zugaldia/cubo/stl/cubo_mounting_plate_vesa.stl

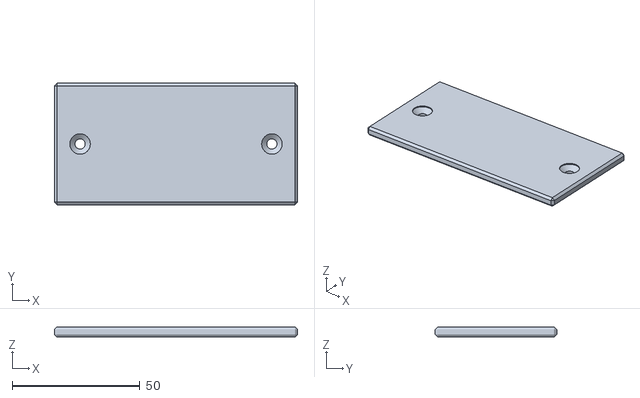
[picture p44: CAD file, 2023-10-19]
stl/cubo_mounting_plate_vesa.stl
95.0 x 47.5 x 4.00
