zugaldia/cubo/stl/cubo_grid_flatiron_small.stl

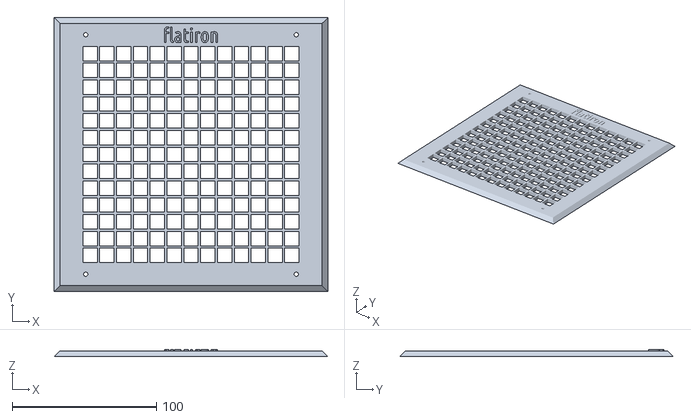
[picture p45: CAD file, 2023-10-19]
stl/cubo_grid_flatiron_small.stl
190.0 x 190.0 x 5.00
