zugaldia/cubo/stl/cubo_generic.stl

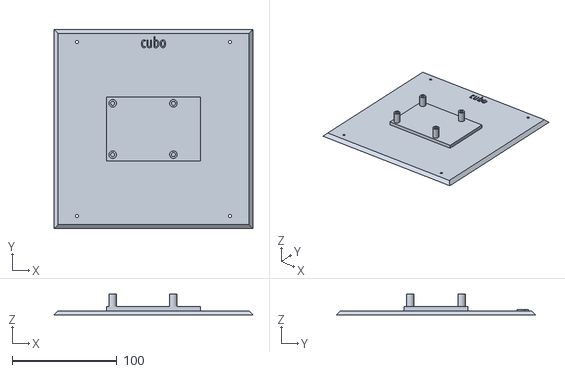
[picture p46: CAD file, 2023-10-19]
stl/cubo_generic.stl
190.0 x 190.0 x 20.0
