zugaldia/cubo/stl/cubo_stand_free_standing.stl

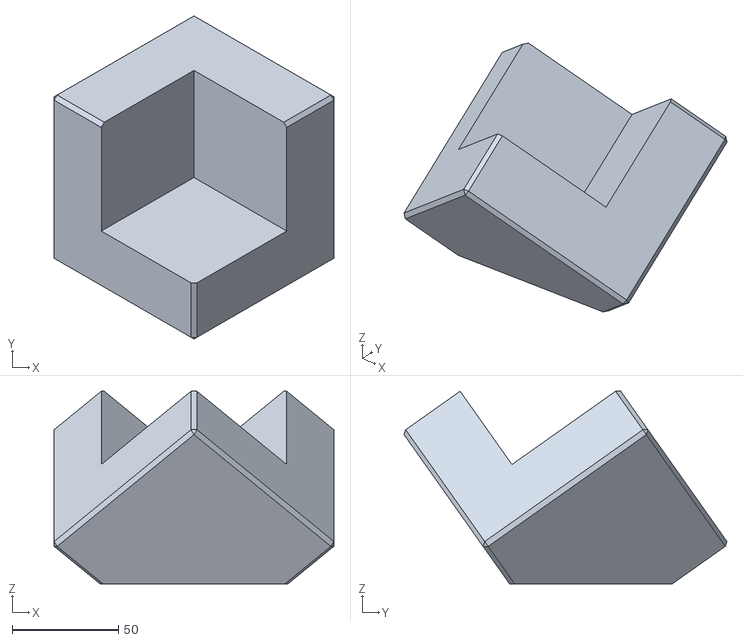
[picture p47: CAD file, 2023-10-19]
stl/cubo_stand_free_standing.stl
131.5 x 151.9 x 90.5
